leehonan/meterman-node/pcb_puck/Puck Back.png

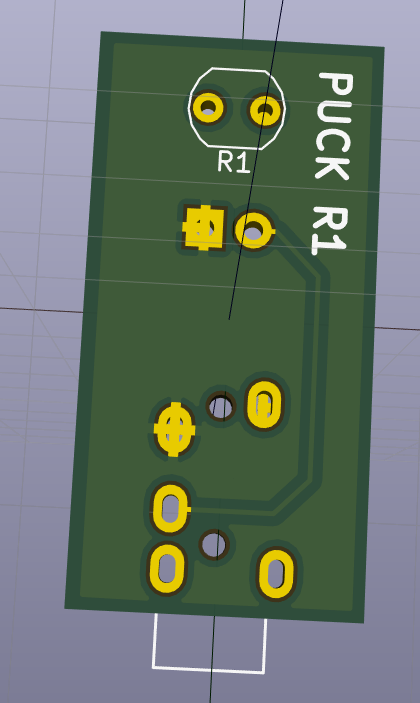
pcb_puck/Puck Back.png
