leehonan/meterman-node/pcb_puck/Puck Front.png

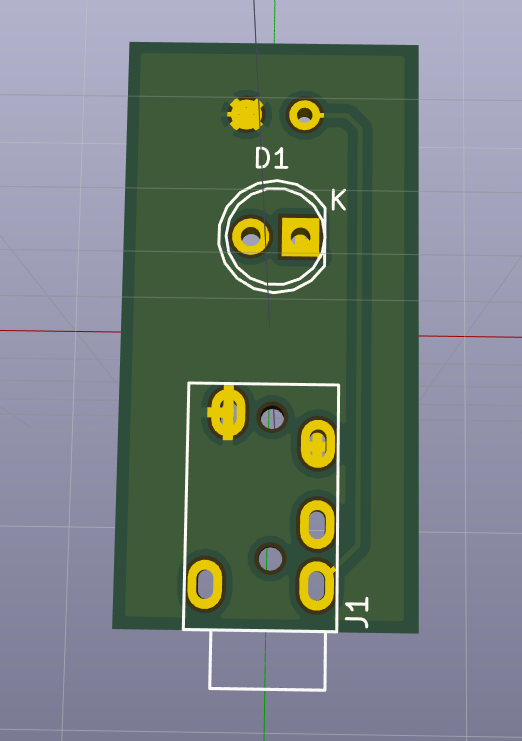
pcb_puck/Puck Front.png
